drewsum/Electronic-Calendar/hdw/design_files/3605.asc

C1: cap; 10n
C2: cap; 2.2µ
C3: cap; .1µ
C4: cap; 62p
C5: cap; 47µ
C6: cap; 47µ
C7: cap; 15p
C8: cap; 15p
C9: cap; 0.1µ
D1: schottky; CMDSH2-3
I1: current; PULSE(0 5 3m 0.1u 0.1u 0.5m 1m); load
L1: ind; 0.47µ
R1: res; 63.4k
R2: res; 100k
R3: res; 22.1k
R4: res; 13.3k
R5: res; 10
U1: LTC3605
V1: voltage; 12
Named nets: 0, IN, INTVCC, OUT
.tran 10m startup
