drewsum/Electronic-Calendar/sfw/U701_firmware/Electronic_Calendar.X/device_control.c

/* ************************************************************************** */
/** Descriptive File Name

  @Company
    Company Name

  @File Name
    filename.c

  @Summary
    Brief description of the file.

  @Description
    Describe the purpose of this file.
 */
/* ************************************************************************** */

#include <xc.h>
#include <stdio.h>
#include <string.h>

#include "device_control.h"
#include "terminal_control.h"

// private function prototype

// this function sets up the PLL
void PLLInitialize(void);

// this function sets up reference clock 1
void REFCLK1Initialize(void);

// this function sets up reference clock 2
void REFCLK2Initialize(void);

// this function sets up reference clock 3
void REFCLK3Initialize(void);

// this function sets up reference clock 4
void REFCLK4Initialize(void);

// this function sets up peripheral bus clock 1
void PBCLK1Initialize(void);

// this function sets up peripheral bus clock 2
void PBCLK2Initialize(void);

// this function sets up peripheral bus clock 3
void PBCLK3Initialize(void);

// this function sets up peripheral bus clock 4
void PBCLK4Initialize(void);

// this function sets up peripheral bus clock 5
void PBCLK5Initialize(void);

// this function sets up peripheral bus clock 7
void PBCLK7Initialize(void);

// this function sets up peripheral bus clock 8
void PBCLK8Initialize(void);

// Unlock system function
// This function unlocks the device so that device parameters can be changed
// and the microcontroller can be reset
inline void deviceUnlock(void) {
    
     // force a lock
    SYSKEY = 0x00000000;
    // write key1 to SYSKEY per datasheet
    SYSKEY = 0xAA996655;
    // write key2 to SYSKEY per datasheet
    SYSKEY = 0x556699AA;
    
}


// Lock system function
// This function re-locks the system so that important device parameters may 
// not be changed
inline void deviceLock(void) {
    
     // write an invalid key to force lock
    SYSKEY = 0x00000000;
    
}

// Rest device function
// This function resets the microcontroller
void deviceReset(void) {
    
    // disable interrupts
    disableGlobalInterrupts();
    
    // unlock the device
    deviceUnlock();
    
    // Arm reset
    RSWRSTSET = 1;
    
    // read RSWRST register to trigger reset
    unsigned int dummy = RSWRST;
    
}

// This function is a software delay that simply counts loops while decrementing
// the argument
inline void softwareDelay(uint32_t inputDelay) {
 
    while (inputDelay > 0) {
        
        Nop();
        inputDelay--;
        
    }
    
}

// This function initializes the oscillator and PLL
// This sets up a SYSCLK of 200 MHz
// REFCLK1: Disabled
// REFCLK2: Disabled
// REFCLK3: Disabled
// REFCLK4: Disabled
// PBCLK1: 66.6 MHz
// PBCLK2: 66.6 MHz
// PBCLK3: 12.5 MHz
// PBCLK4: 66.6 MHz
// PBCLK5: 66.6 MHz
// PBCLK7: 200 MHz
// PBCLK8: 66.6M Hz
void clockInitialize(void) {
 
    // unlock the device
    deviceUnlock();
    
    // unlock clock and PLL settings
    OSCCONbits.CLKLOCK = 0;
    
    // Initialize peripheral bus clocks
    PBCLK1Initialize();
    PBCLK2Initialize();
    PBCLK3Initialize();
    PBCLK4Initialize();
    PBCLK5Initialize();
    PBCLK7Initialize();
    PBCLK8Initialize();

    // Initialize reference clocks
    REFCLK1Initialize();
    REFCLK2Initialize();
    REFCLK3Initialize();
    REFCLK4Initialize();

    // set the FRC divider to 1
    // This sets FRCDIV frequency to 8 MHz
    OSCCONbits.FRCDIV = 0b000;
    
    // Initialize the PLL
    PLLInitialize();
    
    // Set new clock source as SPLL
    OSCCONbits.NOSC = 0b001;
    
    // Initiate clock switch
    OSCCONbits.OSWEN = 1;
    
    // wait for switch to complete
    while (OSCCONbits.OSWEN == 1);
        
    // lock clock and PLL settings
    OSCCONbits.CLKLOCK = 1;
    
    // re-lock the device
    deviceLock();
    
}

// this function sets up the PLL
void PLLInitialize(void) {
 
    // Set PLL input range as 5-10 MHz
    SPLLCONbits.PLLRANGE = 0b001;
    
    // Set the input to the PLL as FRC
    SPLLCONbits.PLLICLK = 1;
    
    // Set PLL input divider to 1
    SPLLCONbits.PLLIDIV = 0b000;
    
    // Set PLL multiplier to 50
    SPLLCONbits.PLLMULT = 0b110001; // (49 in binary, 0b0000000 => PLL X 1)
    
    // Set PLL output divider to 2
    SPLLCONbits.PLLODIV = 0b001;
    
}

// this function sets up reference clock 1
void REFCLK1Initialize(void) {
 
    // Set REFCLK1 divider to 1
    REFO1CONbits.RODIV = 0b000000000000000;
    
    // Disable REFCLK1
    REFO1CONbits.ON = 0;
    
    // Disable REFCLK1 in Idle mode
    REFO1CONbits.SIDL = 1;
    
    // Disable output of REFCLK1 onto output pin
    REFO1CONbits.OE = 0;
    
    // Disable REFCLK1 in sleep
    REFO1CONbits.RSLP = 0;
    
}

// this function sets up reference clock 2
void REFCLK2Initialize(void) {
 
    // Set REFCLK2 divider to 1
    REFO2CONbits.RODIV = 0b000000000000000;
    
    // Disable REFCLK2
    REFO2CONbits.ON = 0;
    
    // Disable REFCLK2 in Idle mode
    REFO2CONbits.SIDL = 1;
    
    // Disable output of REFCLK2 onto output pin
    REFO2CONbits.OE = 0;
    
    // Disable REFCLK2 in sleep
    REFO2CONbits.RSLP = 0;
    
}

// this function sets up reference clock 3
void REFCLK3Initialize(void) {
 
    // Set REFCLK3 divider to 1
    REFO3CONbits.RODIV = 0b000000000000000;
    
    // Disable REFCLK3
    REFO3CONbits.ON = 0;
    
    // Disable REFCLK3 in Idle mode
    REFO3CONbits.SIDL = 1;
    
    // Disable output of REFCLK3 onto output pin
    REFO3CONbits.OE = 0;
    
    // Disable REFCLK3 in sleep
    REFO3CONbits.RSLP = 0;
    
}

// this function sets up reference clock 4
void REFCLK4Initialize(void) {
 
    // Set REFCLK4 divider to 1
    REFO4CONbits.RODIV = 0b000000000000000;
    
    // Disable REFCLK4
    REFO4CONbits.ON = 0;
    
    // Disable REFCLK4 in Idle mode
    REFO4CONbits.SIDL = 1;
    
    // Disable output of REFCLK4 onto output pin
    REFO4CONbits.OE = 0;
    
    // Disable REFCLK4 in sleep
    REFO4CONbits.RSLP = 0;
    
}

// this function sets up peripheral bus clock 1
void PBCLK1Initialize(void) {
 
    // wait for divisor to be ready for change
    while (PB1DIVbits.PBDIVRDY == 0);
    
    // Set PBCLK1 divider to 3
    PB1DIVbits.PBDIV = 0b0000010;
    
    // wait for divisor to be ready for change
    while (PB1DIVbits.PBDIVRDY == 0);
    
    // Enable PBCLK1
    // (PBCLK1 cannot be turned off so the ON bit is hardwired 1 in silicon)
    
}

// this function sets up peripheral bus clock 2
void PBCLK2Initialize(void) {
 
    // wait for divisor to be ready for change
    while (PB2DIVbits.PBDIVRDY == 0);
    
    // Set PBCLK2 divider to 3
    PB2DIVbits.PBDIV = 0b0000010;
    
    // wait for divisor to be ready for change
    while (PB2DIVbits.PBDIVRDY == 0);
    
    // Enable PBCLK2
    PB2DIVbits.ON = 1;
    
}

// this function sets up peripheral bus clock 3
void PBCLK3Initialize(void) {
 
    // wait for divisor to be ready for change
    while (PB3DIVbits.PBDIVRDY == 0);
    
    // Set PBCLK3 divider to 16
    PB3DIVbits.PBDIV = 0b0001111;
    
    // wait for divisor to be ready for change
    while (PB3DIVbits.PBDIVRDY == 0);
    
    // Enable PBCLK3
    PB3DIVbits.ON = 1;
    
}

// this function sets up peripheral bus clock 4
void PBCLK4Initialize(void) {
 
    // wait for divisor to be ready for change
    while (PB4DIVbits.PBDIVRDY == 0);
    
    // Set PBCLK4 divider to 3
    PB4DIVbits.PBDIV = 0b0000010;
    
    // wait for divisor to be ready for change
    while (PB4DIVbits.PBDIVRDY == 0);
    
    // Enable PBCLK4
    PB4DIVbits.ON = 1;
    
}

// this function sets up peripheral bus clock 5
void PBCLK5Initialize(void) {
 
    // wait for divisor to be ready for change
    while (PB5DIVbits.PBDIVRDY == 0);
    
    // Set PBCLK5 divider to 3
    PB5DIVbits.PBDIV = 0b0000010;
    
    // wait for divisor to be ready for change
    while (PB5DIVbits.PBDIVRDY == 0);
    
    // Enable PBCLK5
    PB5DIVbits.ON = 1;
    
}

// this function sets up peripheral bus clock 7
void PBCLK7Initialize(void) {

    // wait for divisor to be ready for change
    while (PB7DIVbits.PBDIVRDY == 0);
    
    // Set PBCLK7 divider to 1
    PB7DIVbits.PBDIV = 0b0000000;
    
    // wait for divisor to be ready for change
    while (PB7DIVbits.PBDIVRDY == 0);
    
    // Enable PBCLK7
    PB7DIVbits.ON = 1;
    
}

// this function sets up peripheral bus clock 8
void PBCLK8Initialize(void) {
 
    // wait for divisor to be ready for change
    while (PB8DIVbits.PBDIVRDY == 0);
    
    // Set PBCLK8 divider to 3
    PB8DIVbits.PBDIV = 0b00000010;
    
    // wait for divisor to be ready for change
    while (PB8DIVbits.PBDIVRDY == 0);
    
    // Enable PBCLK8
    PB8DIVbits.ON = 1;
    
}

// This function returns a formatted string of the clock setting
char * stringFromClockSetting(uint32_t clock_integer) {
    
    static char return_string[20];
    
    if (clock_integer >= 1000000) {
     
        sprintf(return_string, "%.2f MHz", clock_integer / 1000000.0);
        
    }
    
    else if (clock_integer >= 1000) {
     
        sprintf(return_string, "%.2f kHz", clock_integer / 1000.0);
        
    }
    
    else if (clock_integer > 0) {
     
        sprintf(return_string, "%.2f Hz", (float) clock_integer);
        
    }
    
    else if (clock_integer == 0) {
     
        sprintf(return_string, "Disabled");
        
    }
    
    return return_string;
    
}


// This function unlocks peripheral pin select
// THIS CAN ONLY BE CALLED ONCE PER DEVICE RESET!!!
void PPSUnlock(void) {

    // Unlock device
    deviceUnlock();
    
    // Unlock PPS
    CFGCONbits.IOLOCK = 0;
    
    // Lock device
    deviceLock();
    
}

// This function locks peripheral pin select
void PPSLock(void) {
    
    // Unlock device
    deviceUnlock();
    
    // Lock PPS
    CFGCONbits.IOLOCK = 1;
    
    // Lock device
    deviceLock();
    
}

// This function unlocks peripheral module disable
void PMDUnlock(void) {
    
    // Unlock device
    deviceUnlock();
    
    // Unlock PMD
    CFGCONbits.PMDLOCK = 0;
    
    // Lock device
    deviceLock();
    
}

// This function locks peripheral module disable
void PMDLock(void) {
    
    // Unlock device
    deviceUnlock();
    
    // Lock PMD
    CFGCONbits.PMDLOCK = 1;
    
    // Lock device
    deviceLock();
    
}

// This function returns a string containing the device's serial number
char * getStringSerialNumber(void) {
 
    static char return_string[20];
    
    sprintf(return_string, "0x%X%X",
        *((uint32_t *)(0xBFC54024)),
        *((uint32_t *)(0xBFC54020)));
    
    return return_string;
    
}

// This function returns a 32 bit device ID
uint32_t getDeviceID(void) {
 
    return *((uint32_t *)(0xBF800020)) & 0x0FFFFFFF;
    
}

// This function returns a string with the part number of the device from the device ID
char * getDeviceIDString(uint32_t device_ID) {
 
    switch (device_ID) {
     
        case 0x7201053:
            return "PIC32MZ0512EFE064";
            break;
            
        case 0x7206053:
            return "PIC32MZ0512EFF064";
            break;
            
        case 0x722E053:
            return "PIC32MZ0512EFK064";
            break;
            
        case 0x7202053:
            return "PIC32MZ1024EFE064";
            break;
            
        case 0x7207053:
            return "PIC32MZ1024EFF064";
            break;
            
        case 0x722F053:
            return "PIC32MZ1024EFK064";
            break;
            
        case 0x7203053:
            return "PIC32MZ1024EFG064";
            break;
            
        case 0x7208053:
            return "PIC32MZ1024EFH064";
            break;
            
        case 0x7230053:
            return "PIC32MZ1024EFM064";
            break;
            
        case 0x7204053:
            return "PIC32MZ2048EFG064";
            break;
            
        case 0x7209053:
            return "PIC32MZ2048EFH064";
            break;
            
        case 0x7231053:
            return "PIC32MZ2048EFM064";
            break;
            
        case 0x720B053:
            return "PIC32MZ0512EFE100";
            break;
            
        case 0x7210053:
            return "PIC32MZ0512EFF100";
            break;
            
        case 0x7238053:
            return "PIC32MZ0512EFK100";
            break;
            
        case 0x720C053:
            return "PIC32MZ1024EFE100";
            break;
            
        case 0x7211053:
            return "PIC32MZ1024EFF100";
            break;
            
        case 0x7239053:
            return "PIC32MZ1024EFK100";
            break;
            
        case 0x720D053:
            return "PIC32MZ1024EFG100";
            break;
            
        case 0x7212053:
            return "PIC32MZ1024EFH100";
            break;
            
        case 0x723A053:
            return "PIC32MZ1024EFM100";
            break;
            
        case 0x720E053:
            return "PIC32MZ2048EFG100";
            break;
            
        case 0x7213053:
            return "PIC32MZ2048EFH100";
            break;
            
        case 0x723B053:
            return "PIC32MZ2048EFM100";
            break;
            
        case 0x7215053:
            return "PIC32MZ0512EFE124";
            break;
            
        case 0x721A053:
            return "PIC32MZ0512EFF124";
            break;
            
        case 0x7242053:
            return "PIC32MZ0512EFK124";
            break;
            
        case 0x7216053:
            return "PIC32MZ1024EFE124";
            break;
            
        case 0x721B053:
            return "PIC32MZ1024EFF124";
            break;
            
        case 0x7243053:
            return "PIC32MZ1024EFK124";
            break;
            
        case 0x7217053:
            return "PIC32MZ1024EFG124";
            break;
            
        case 0x721C053:
            return "PIC32MZ1024EFH124";
            break;
            
        case 0x7244053:
            return "PIC32MZ1024EFM124";
            break;
            
        case 0x7218053:
            return "PIC32MZ2048EFG124";
            break;
            
        case 0x721D053:
            return "PIC32MZ2048EFH124";
            break;
            
        case 0x7245053:
            return "PIC32MZ2048EFM124";
            break;
            
        case 0x721F053:
            return "PIC32MZ0512EFE144";
            break;
            
        case 0x7224053:
            return "PIC32MZ0512EFF144";
            break;
            
        case 0x724C053:
            return "PIC32MZ0512EFK144";
            break;
            
        case 0x7220053:
            return "PIC32MZ1024EFE144";
            break;
            
        case 0x7225053:
            return "PIC32MZ1024EFF144";
            break;
            
        case 0x724D053:
            return "PIC32MZ1024EFK144";
            break;
            
        case 0x7221053:
            return "PIC32MZ1024EFG144";
            break;
            
        case 0x7226053:
            return "PIC32MZ1024EFH144";
            break;
            
        case 0x724E053:
            return "PIC32MZ1024EFM144";
            break;
            
        case 0x7222053:
            return "PIC32MZ2048EFG144";
            break;
            
        case 0x7227053:
            return "PIC32MZ2048EFH144";
            break;
            
        case 0x724F053:
            return "PIC32MZ2048EFM144";
            break;
            
        default:
            return "Undefined";
            break;
        
    }
    
}

// This function returns an 8 bit revision ID
uint8_t getRevisionID(void) {
 
    return *((uint32_t *)(0xBF800020)) & 0xF0000000 >> 28;
    
}

// This function returns a string with the revision ID
char * getRevisionIDString(uint8_t revision_ID) {
 
    switch (revision_ID) {
    
        case 0x1:
            return "A1";
            break;
            
        case 0x3:
            return "A3";
            break;
            
        case 0x6:
            return "B2";
            break;
            
        default:
            return "Undefined";
            break;
        
    }
    
}

// This function prints clock settings, requires a given input sysclk
void printClockStatus(uint32_t input_sysclk) {

    terminalTextAttributesReset();
    terminalTextAttributes(GREEN_COLOR, BLACK_COLOR, BOLD_FONT);
    
    // Print table heading
    printf("System Clock Settings:\n\r");

    terminalTextAttributes(GREEN_COLOR, BLACK_COLOR, NORMAL_FONT);
    // Print SYSCLK setting
    printf("    SYSCLK (System Clock) is set to: %s\n\r",
            stringFromClockSetting(input_sysclk));
    
    // Print current oscillator configuration
    printf("\n\r    Current Oscillator Selections is: ");
    switch (OSCCONbits.COSC) {
     
        case 0b000:
            printf("Internal Fast RC (FRC) Oscillator divided by FRCDIV<2:0> bits (FRCDIV)\n\r");
            break;
            
        case 0b001:
            printf("System PLL (SPLL)\n\r");
            break;
            
        case 0b010:
            printf("Primary Oscillator (POSC) (HS or EC)\n\r");
            break;
            
        case 0b100:
            printf("Secondary Oscillator (SOSC)\n\r");
            break;
            
        case 0b101:
            printf("Internal Low-Power RC (LPRC) Oscillator\n\r");
            break;
            
        case 0b110:
            terminalTextAttributes(RED_COLOR, BLACK_COLOR, BOLD_FONT);
            printf("Back-up Fast RC (BFRC) Oscillator\n\r");
            terminalTextAttributesReset();
            
            break;
            
        case 0b111:
            printf("Internal Fast RC (FRC) Oscillator divided by FRCDIV<2:0> bits (FRCDIV)\n\r");
            break;
        
    }
    
    // Print dream mode status
    if (OSCCONbits.DRMEN) terminalTextAttributes(GREEN_COLOR, BLACK_COLOR, NORMAL_FONT);
    else terminalTextAttributes(RED_COLOR, BLACK_COLOR, NORMAL_FONT);
    printf("\n\r    Dream Mode %s\n\r", OSCCONbits.DRMEN ? "Enabled" : "Disabled");
    
    // Print boot PLL status
    terminalTextAttributes(GREEN_COLOR, BLACK_COLOR, NORMAL_FONT);
    printf("\n\r    Boot PLL Input Divider is set to: %d\n\r", (DEVCFG2bits.FPLLIDIV + 1));
    printf("    Boot PLL Multiplier is set to: %d\n\r", (DEVCFG2bits.FPLLMULT + 1));
    printf("    Boot PLL Output Divider is set to: %d\n\r", (DEVCFG2bits.FPLLODIV + 1));
    
    printf("    Overall Boot PLL Gain is: %.3f\n\r", 
            (float) (DEVCFG2bits.FPLLMULT + 1) / ((DEVCFG2bits.FPLLIDIV) + (DEVCFG2bits.FPLLODIV) + 1));
    
    
    // Print changed PLL status
    terminalTextAttributes(GREEN_COLOR, BLACK_COLOR, NORMAL_FONT);
    printf("\n\r    Operational PLL Input Divider is set to: %d\n\r", (SPLLCONbits.PLLIDIV + 1));
    printf("    Operational PLL Multiplier is set to: %d\n\r", (SPLLCONbits.PLLMULT + 1));
    printf("    Operational PLL Output Divider is set to: %d\n\r", (SPLLCONbits.PLLODIV + 1));
    
    printf("    Overall Operational PLL Gain is: %.3f\n\r", 
            (float) (SPLLCONbits.PLLMULT + 1) / ((SPLLCONbits.PLLIDIV) + (SPLLCONbits.PLLODIV) + 1));
    
    
    // Determine refclk1
    if (REFO1CONbits.ON == 0) {
     
        terminalTextAttributes(RED_COLOR, BLACK_COLOR, NORMAL_FONT);
        printf("\n\r    REFCLK1 (Reference Clock 1) Disabled\n\r");
        
    }
    
    else {
     
        terminalTextAttributes(GREEN_COLOR, BLACK_COLOR, NORMAL_FONT);
        printf("    REFCLK1 (Reference Clock 1) is set to: %s\n\r",
                stringFromClockSetting(input_sysclk / (REFO1CONbits.RODIV + 1)));
        
    }
    
    // Determine refclk2
    if (REFO2CONbits.ON == 0) {
     
        terminalTextAttributes(RED_COLOR, BLACK_COLOR, NORMAL_FONT);
        printf("    REFCLK2 (Reference Clock 2) Disabled\n\r");
        
    }
    
    else {
     
        terminalTextAttributes(GREEN_COLOR, BLACK_COLOR, NORMAL_FONT);
        printf("    REFCLK2 (Reference Clock 2) is set to: %s\n\r",
                stringFromClockSetting(input_sysclk / (REFO2CONbits.RODIV + 1)));
        
    }
    
    // Determine refclk3
    if (REFO3CONbits.ON == 0) {
     
        terminalTextAttributes(RED_COLOR, BLACK_COLOR, NORMAL_FONT);
        printf("    REFCLK3 (Reference Clock 3) Disabled\n\r");
        
    }
    
    else {
     
        terminalTextAttributes(GREEN_COLOR, BLACK_COLOR, NORMAL_FONT);
        printf("    REFCLK3 (Reference Clock 3) is set to: %s\n\r",
                stringFromClockSetting(input_sysclk / (REFO3CONbits.RODIV + 1)));
        
    }
    
    // Determine refclk4
    if (REFO4CONbits.ON == 0) {
     
        terminalTextAttributes(RED_COLOR, BLACK_COLOR, NORMAL_FONT);
        printf("    REFCLK4 (Reference Clock 4) Disabled\n\r");
        
    }
    
    else {
     
        terminalTextAttributes(GREEN_COLOR, BLACK_COLOR, NORMAL_FONT);
        printf("    REFCLK4 (Reference Clock 4) is set to: %s\n\r",
                stringFromClockSetting(input_sysclk / (REFO4CONbits.RODIV + 1)));
        
    }
    
    terminalTextAttributes(GREEN_COLOR, BLACK_COLOR, NORMAL_FONT);
    
    // Determine PBCLK1 (Cannot be disabled)
    printf("\n\r    PBCLK1 (Peripheral Bus Clock 1) is set to: %s\n\r",
            stringFromClockSetting(input_sysclk / (PB1DIVbits.PBDIV + 1)));
    
    // Determine PBCLK2
    printf("    PBCLK2 (Peripheral Bus Clock 2) is set to: %s\n\r",
            stringFromClockSetting(input_sysclk / (PB2DIVbits.PBDIV + 1)));
    
    // Determine PBCLK3
    printf("    PBCLK3 (Peripheral Bus Clock 3) is set to: %s\n\r",
            stringFromClockSetting(input_sysclk / (PB3DIVbits.PBDIV + 1)));
    
    // Determine PBCLK4
    printf("    PBCLK4 (Peripheral Bus Clock 4) is set to: %s\n\r",
            stringFromClockSetting(input_sysclk / (PB4DIVbits.PBDIV + 1)));

    // Determine PBCLK5
    printf("    PBCLK5 (Peripheral Bus Clock 5) is set to: %s\n\r",
            stringFromClockSetting(input_sysclk / (PB5DIVbits.PBDIV + 1)));
    
    // No PBCLK6
    terminalTextAttributes(RED_COLOR, BLACK_COLOR, NORMAL_FONT);
    printf("    No Peripheral Bus Clock 6 Present\n\r");
    
    // Determine PBCLK7
    terminalTextAttributes(GREEN_COLOR, BLACK_COLOR, NORMAL_FONT);
    printf("    PBCLK7 (Peripheral Bus Clock 7) is set to: %s\n\r",
            stringFromClockSetting(input_sysclk / (PB7DIVbits.PBDIV + 1)));
    
    // Determine PBCLK8
    printf("    PBCLK8 (Peripheral Bus Clock 8) is set to: %s\n\r",
            stringFromClockSetting(input_sysclk / (PB8DIVbits.PBDIV + 1)));
    
    // Print clock lock status
    if (OSCCONbits.CLKLOCK) terminalTextAttributes(GREEN_COLOR, BLACK_COLOR, NORMAL_FONT);
    else terminalTextAttributes(RED_COLOR, BLACK_COLOR, NORMAL_FONT);
    printf("\n\r    Clock Lock: %s\n\r", OSCCONbits.CLKLOCK ? "Enabled" : "Disabled");
    
    // Print clock failure status
    if (OSCCONbits.CF) terminalTextAttributes(RED_COLOR, BLACK_COLOR, NORMAL_FONT);
    else terminalTextAttributes(GREEN_COLOR, BLACK_COLOR, NORMAL_FONT);
    printf("\n\r    Clock Fail: %s\n\r", OSCCONbits.CF ? "Detected" : "Not Detected");
    
    // Print Sleep Mode status
    terminalTextAttributes(GREEN_COLOR, BLACK_COLOR, NORMAL_FONT);
    printf("\n\r    WAIT instruction enters: %s Mode\n\r", OSCCONbits.CF ? "Sleep" : "Idle");
    
    // Print status of oscillators that are ready
    if (CLKSTATbits.LPRCRDY) terminalTextAttributes(GREEN_COLOR, BLACK_COLOR, NORMAL_FONT);
    else terminalTextAttributes(RED_COLOR, BLACK_COLOR, NORMAL_FONT);
    printf("\n\r    LPRC Oscillator Status: %s\n\r", CLKSTATbits.LPRCRDY ? "Ready" : "Not Ready");
    if (CLKSTATbits.SOSCRDY) terminalTextAttributes(GREEN_COLOR, BLACK_COLOR, NORMAL_FONT);
    else terminalTextAttributes(RED_COLOR, BLACK_COLOR, NORMAL_FONT);
    printf("    SOSC Oscillator Status: %s\n\r", CLKSTATbits.SOSCRDY ? "Ready" : "Not Ready");
    if (CLKSTATbits.POSCRDY) terminalTextAttributes(GREEN_COLOR, BLACK_COLOR, NORMAL_FONT);
    else terminalTextAttributes(RED_COLOR, BLACK_COLOR, NORMAL_FONT);
    printf("    POSC Oscillator Status: %s\n\r", CLKSTATbits.POSCRDY ? "Ready" : "Not Ready");
    if (CLKSTATbits.DIVSPLLRDY) terminalTextAttributes(GREEN_COLOR, BLACK_COLOR, NORMAL_FONT);
    else terminalTextAttributes(RED_COLOR, BLACK_COLOR, NORMAL_FONT);
    printf("    SPLL Oscillator Status: %s\n\r", CLKSTATbits.DIVSPLLRDY ? "Ready" : "Not Ready");
    if (CLKSTATbits.FRCRDY) terminalTextAttributes(GREEN_COLOR, BLACK_COLOR, NORMAL_FONT);
    else terminalTextAttributes(RED_COLOR, BLACK_COLOR, NORMAL_FONT);
    printf("    FRC Oscillator Status: %s\n\r", CLKSTATbits.FRCRDY ? "Ready" : "Not Ready");

    terminalTextAttributesReset();

}

// This function initializes the random number generator
void RNGInitialize(void) {
 
    // Enable ring oscillator bias correction mode
    RNGCONbits.TRNGMODE = 1;
    
    // Change numbers continously
    RNGCONbits.CONT = 1;
    
    // Enable both TRNG and PRNG
    RNGCONbits.TRNGEN = 1;
    RNGCONbits.PRNGEN = 1;
    
    // Load seed
    RNGCONbits.LOAD = 1;
    
}
