drewsum/Electronic-Calendar/sfw/U701_firmware/Electronic_Calendar.X/calendar_leds.c

#include "calendar_leds.h"

// this function updates the month LEDs to reflect the month passed to it
void updateMonthLEDs(month_t input_month) {
 
    nJAN_LED_PIN = HIGH;
    nFEB_LED_PIN = HIGH;
    nMAR_LED_PIN = HIGH;
    nAPR_LED_PIN = HIGH;
    nMAY_LED_PIN = HIGH;
    nJUN_LED_PIN = HIGH;
    nJUL_LED_PIN = HIGH;
    nAUG_LED_PIN = HIGH;
    nSEP_LED_PIN = HIGH;
    nOCT_LED_PIN = HIGH;
    nNOV_LED_PIN = HIGH;
    nDEC_LED_PIN = HIGH;
    
    // decide what LEDs to turn on based on input_month
    switch (input_month) {
    
        case January:
            nJAN_LED_PIN = LOW;
            break;
            
        case February:
            nFEB_LED_PIN = LOW;
            break;
            
        case March:
            nMAR_LED_PIN = LOW;
            break;
            
        case April:
            nAPR_LED_PIN = LOW;
            break;
            
        case May:
            nMAY_LED_PIN = LOW;
            break;
            
        case June:
            nJUN_LED_PIN = LOW;
            break;
            
        case July:
            nJUL_LED_PIN = LOW;
            break;
            
        case August:
            nAUG_LED_PIN = LOW;
            break;
            
        case September:
            nSEP_LED_PIN = LOW;
            break;
            
        case October:
            nOCT_LED_PIN = LOW;
            break;
            
        case November:
            nNOV_LED_PIN = LOW;
            break;
            
        case December:
            nDEC_LED_PIN = LOW;
            break;
            
        default:
            nJAN_LED_PIN = HIGH;
            nFEB_LED_PIN = HIGH;
            nMAR_LED_PIN = HIGH;
            nAPR_LED_PIN = HIGH;
            nMAY_LED_PIN = HIGH;
            nJUN_LED_PIN = HIGH;
            nJUL_LED_PIN = HIGH;
            nAUG_LED_PIN = HIGH;
            nSEP_LED_PIN = HIGH;
            nOCT_LED_PIN = HIGH;
            nNOV_LED_PIN = HIGH;
            nDEC_LED_PIN = HIGH;
            break;
            
    }
    
}

// this function updates the weekday LEDs to reflect the weekday passed
void updateWeekdayLEDs(weekday_t input_weekday) {
 
    nSUN_LED_PIN = HIGH;
    nMON_LED_PIN = HIGH;
    nTUE_LED_PIN = HIGH;
    nWED_LED_PIN = HIGH;
    nTHUR_LED_PIN = HIGH;
    nFRI_LED_PIN = HIGH;
    nSAT_LED_PIN = HIGH;
    
    // determine IO settings based on input_weekday
    switch (input_weekday) {
    
        case Sunday:
            nSUN_LED_PIN = LOW;
            break;
            
        case Monday:
            nMON_LED_PIN = LOW;
            break;
            
        case Tuesday:
            nTUE_LED_PIN = LOW;
            break;
            
        case Wednesday:
            nWED_LED_PIN = LOW;
            break;
            
        case Thursday:
            nTHUR_LED_PIN = LOW;
            break;
            
        case Friday:
            nFRI_LED_PIN = LOW;
            break;
        
        case Saturday:
            nSAT_LED_PIN = LOW;
            break;
            
        default:
            nSUN_LED_PIN = HIGH;
            nMON_LED_PIN = HIGH;
            nTUE_LED_PIN = HIGH;
            nWED_LED_PIN = HIGH;
            nTHUR_LED_PIN = HIGH;
            nFRI_LED_PIN = HIGH;
            nSAT_LED_PIN = HIGH;
            break;
            
    }
    
}

// this function updates the year LEDs to indicate the year passed
void updateYearLEDs(uint16_t input_year) {
 
    switch (input_year) {
    
        case 2019:
            YEAR_B0_PIN = LOW;
            YEAR_B1_PIN = LOW;
            YEAR_B2_PIN = LOW;
            break;
            
        case 2020:
            YEAR_B0_PIN = HIGH;
            YEAR_B1_PIN = LOW;
            YEAR_B2_PIN = LOW;
            break;
        
        case 2021:
            YEAR_B0_PIN = LOW;
            YEAR_B1_PIN = HIGH;
            YEAR_B2_PIN = LOW;
            break;
            
        case 2022:
            YEAR_B0_PIN = HIGH;
            YEAR_B1_PIN = HIGH;
            YEAR_B2_PIN = LOW;
            break;
            
        case 2023:
            YEAR_B0_PIN = LOW;
            YEAR_B1_PIN = LOW;
            YEAR_B2_PIN = HIGH;
            break;
            
        case 2024:
            YEAR_B0_PIN = HIGH;
            YEAR_B1_PIN = LOW;
            YEAR_B2_PIN = HIGH;
            break;
            
        case 2025:
            YEAR_B0_PIN = LOW;
            YEAR_B1_PIN = HIGH;
            YEAR_B2_PIN = HIGH;
            break;
            
        case 2026:
            YEAR_B0_PIN = HIGH;
            YEAR_B1_PIN = HIGH;
            YEAR_B2_PIN = HIGH;
            break;
    
        default:
            YEAR_B0_PIN = LOW;
            YEAR_B1_PIN = LOW;
            YEAR_B2_PIN = LOW;
            break;
            
    }
    
}

// this function updates the day LEDs to indicate date passed
void updateDateLEDs(uint8_t input_day) {

    // determine settings based on input_day
    switch (input_day) {
     
        case 1:
            nDATE_DECODE_1_PIN  = LOW;
            nDATE_DECODE_2_PIN  = HIGH;
            nDATE_DECODE_3_PIN  = HIGH;
            nDATE_DECODE_4_PIN  = HIGH;
            DATE_B0_PIN         = LOW;
            DATE_B1_PIN         = LOW;
            DATE_B2_PIN         = LOW;
            break;
            
        case 2:
            nDATE_DECODE_1_PIN  = LOW;
            nDATE_DECODE_2_PIN  = HIGH;
            nDATE_DECODE_3_PIN  = HIGH;
            nDATE_DECODE_4_PIN  = HIGH;
            DATE_B0_PIN         = HIGH;
            DATE_B1_PIN         = LOW;
            DATE_B2_PIN         = LOW;
            break;    
            
        case 3:
            nDATE_DECODE_1_PIN  = LOW;
            nDATE_DECODE_2_PIN  = HIGH;
            nDATE_DECODE_3_PIN  = HIGH;
            nDATE_DECODE_4_PIN  = HIGH;
            DATE_B0_PIN         = LOW;
            DATE_B1_PIN         = HIGH;
            DATE_B2_PIN         = LOW;
            break;
            
        case 4:
            nDATE_DECODE_1_PIN  = LOW;
            nDATE_DECODE_2_PIN  = HIGH;
            nDATE_DECODE_3_PIN  = HIGH;
            nDATE_DECODE_4_PIN  = HIGH;
            DATE_B0_PIN         = HIGH;
            DATE_B1_PIN         = HIGH;
            DATE_B2_PIN         = LOW;
            break;
            
        case 5:
            nDATE_DECODE_1_PIN  = LOW;
            nDATE_DECODE_2_PIN  = HIGH;
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
            nDATE_DECODE_2_PIN  = HIGH;
            nDATE_DECODE_3_PIN  = HIGH;
            nDATE_DECODE_4_PIN  = HIGH;
            DATE_B0_PIN         = LOW;
            DATE_B1_PIN         = LOW;
            DATE_B2_PIN         = LOW;
            break;
            
    }
    
}
