drewsum/Electronic-Calendar/sfw/U701_firmware/Electronic_Calendar.X/heartbeat_timer.c

#include <xc.h>

#include <stdio.h>

#include "heartbeat_timer.h"
#include "error_handler.h"
#include "mcp9804_temp_sensor.h"

// This function initializes the heartbeat timer
void heartbeatTimerInitialize(void) {
    
    // Stop timer 1
    T1CONbits.ON = 0;
    
    // Set timer 1 prescalar to 256
    T1CONbits.TCKPS = 0b11;
    
    // Set timer clock input as PBCLK3
    T1CONbits.TCS = 0;
    
    // Clear timer 1
    TMR1 = 0x0000;
    
    // Set timer 1 period match to 48828
    // This will give an interrupt rate of 1 Hz
    PR1 = 48828;
    
    // Clear Timer1 Interrupt Flag
    clearInterruptFlag(Timer1);
    
    // Set Timer 1 interrupt priority
    setInterruptPriority(Timer1, 6);
    setInterruptSubpriority(Timer1, 3);
    
    // Clear on time counter
    device_on_time_counter = 0;
    
    // Enable timer 1 interrupt
    enableInterrupt(Timer1);
    
    // Start timer 1
    T1CONbits.ON = 1;

}

// This function starts the heartbeat timer
void heartbeatTimerStart(void) {
    
    // Start timer 1
    T1CONbits.ON = 1;
    
}

// This function stops the heartbeat timer
void heartbeatTimerStop(void) {
 
    // Stop timer 1
    T1CONbits.ON = 0;
    
}

// Heartbeat timer interrupt service routine
void __ISR(_TIMER_1_VECTOR, IPL6SRS) hearbeatTimerISR(void) {

    // Clear the watchdog timer
    kickTheDog();
    
    // Clear the deadman timer
    holdThumbTighter();
    
    // Check to see if DMT actually cleared
    verifyThumbTightEnough();

    // Toggle heartbeat LED
    HEARTBEAT_LED_PIN = !(HEARTBEAT_LED_PIN);
    
    // Update error LEDs based on error handler status
    update_error_leds_flag = 1;
    
    // Increment on time counter
    device_on_time_counter++;
        
    // reset temp I2C peripheral, per device errata
    if (getTempI2COnState) tempI2COnStateReset();
    
    // request new temp sensor data
    MCP9804_start_flag = 1;
        
    // clear Timer 1
    TMR1 = 0;
    
    // Clear interrupt flag
    clearInterruptFlag(Timer1);
    
}
