drewsum/Electronic-Calendar/sfw/U701_firmware/Electronic_Calendar.X/power_saving.h

/* ************************************************************************** */
/** Power Saving

  @Company
 Marquette Senior Design E44 2018-2019

  @File Name
    power_saving.h

  @Summary
 Gives APIs for disabling unused peripherals and entering/exiting sleep mode, etc

 */
/* ************************************************************************** */

#ifndef _POWER_SAVING_H    /* Guard against multiple inclusion */
#define _POWER_SAVING_H

#include <xc.h>

#include "device_control.h"

// These are macros needed for defining ISRs, included in XC32
#include <sys/attribs.h>

uint32_t pushbutton_shutdown_request = 0;   // this flag is set when we want to shutdown due to a pushbutton press
uint32_t pushbutton_wakeup_request = 0;   // this flag is set when we want to wake up due to a pushbutton press
uint32_t sleep_state = 0;

// This function disables unused peripherals on startup for power savings
// THIS FUNCTION CAN ONLY BE CALLED ONCE DUE TO PMD LOCKOUT AFTER ONE WRITE SESSION
void PMDInitialize(void);

// This function prints the status of PMD settings
void printPMDStatus(void);

// this function initializes INT2 for use with the cap touch power toggle pushbutton
void capTouchPowerInitialize(void);

// This function initializes the heartbeat timer
void powerToggleDebounceTimerIntialize(void);

// this is the cap touch power toggle button interrupt service routine
void __ISR(_EXTERNAL_2_VECTOR, IPL7SRS) capTouchPowerToggleISR(void);

// this function shuts down the MCU when the power toggle button is pressed
void capToughPowerToggleShutdown(void);

// this function wakes up the MCU when the power toggle button is pressed
void capToughPowerToggleWakeup(void);

#endif /* _POWER_SAVING_H */

/* *****************************************************************************
 End of File
 */
